kb1dds/AM27S19_eprom_programmer/schematic.kicad_sch

## KiCad design schematic.kicad_sch (2024-02-24)

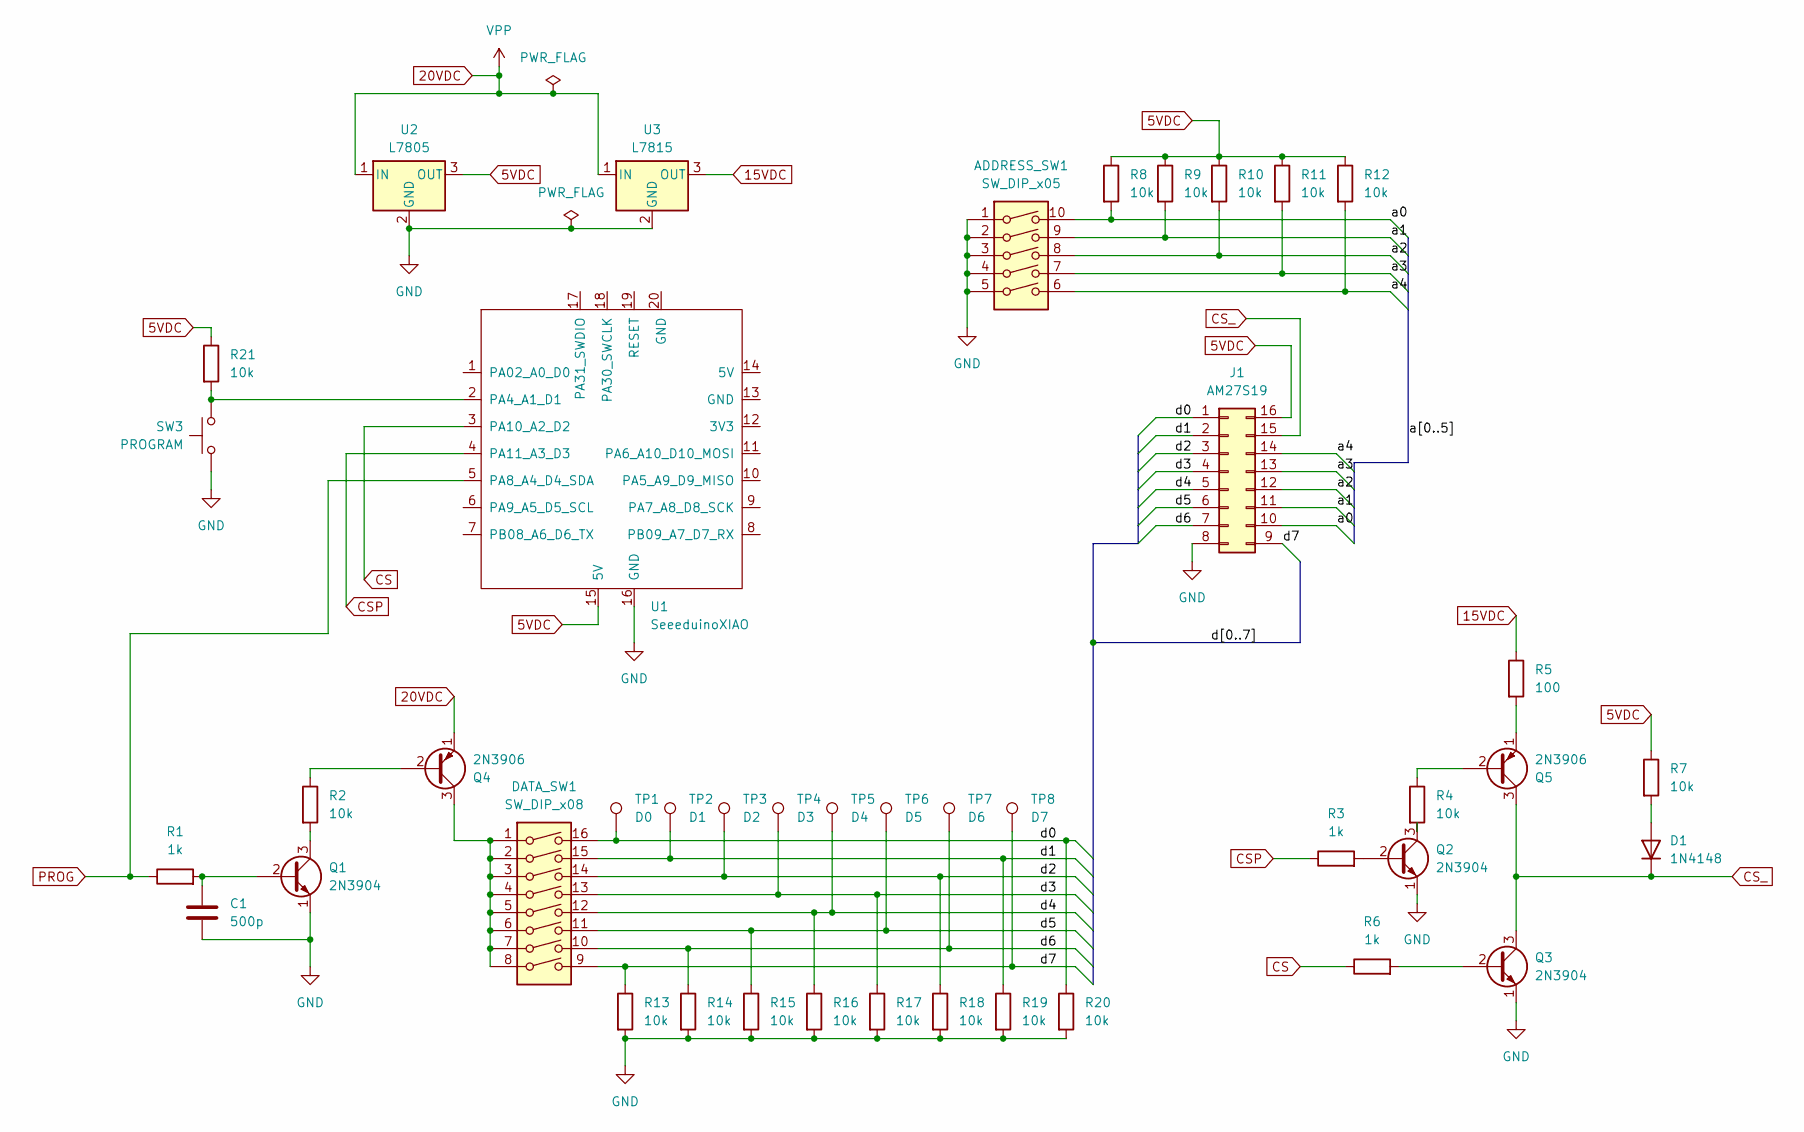
[picture p3: schematic schematic.kicad_sch]

Parts:
ADDRESS_SW1: SW_DIP_x05
C1: 500p
D1: 1N4148; D_DO-35_SOD27_P7.62mm_Horizontal
DATA_SW1: SW_DIP_x08
J1: AM27S19
Q1, Q2, Q3: 2N3904; TO-92_Inline
Q4, Q5: 2N3906; TO-92_Inline
R1, R3, R6: 1k
R2, R4, R7, R8, R9, R10, R11, R12, R13, R14, R15, R16, R17, R18, R19, R20, R21: 10k
R5: 100
SW3: PROGRAM
TP1: D0
TP2: D1
TP3: D2
TP4: D3
TP5: D4
TP6: D5
TP7: D6
TP8: D7
U1: SeeeduinoXIAO
U2: L7805
U3: L7815

Connections:
5VDC: J1.16, R7.1, R8.1, R9.1, R10.1, R11.1, R12.1, R21.1, U1.15 (5V), U2.3 (OUT)
15VDC: R5.1, U3.3 (OUT)
20VDC: Q4.1 (E), U2.1 (IN), U3.1 (IN)
CS: R6.1, U1.3 (PA10_A2_D2)
CSP: R3.1, U1.4 (PA11_A3_D3)
CS_: D1.1 (K), J1.15, Q3.3 (C), Q5.3 (C)
GND: ADDRESS_SW1.1, ADDRESS_SW1.2, ADDRESS_SW1.3, ADDRESS_SW1.4, ADDRESS_SW1.5, C1.2, J1.8, Q1.1 (E), Q2.1 (E), Q3.1 (E), R13.2, R14.2, R15.2, R16.2, R17.2, R18.2, R19.2, R20.2, SW3.2, U1.16 (GND), U2.2 (GND), U3.2 (GND)
unnamed: C1.1, Q1.2 (B), R1.2
unnamed: D1.2 (A), R7.2
unnamed: DATA_SW1.1, DATA_SW1.2, DATA_SW1.3, DATA_SW1.4, DATA_SW1.5, DATA_SW1.6, DATA_SW1.7, DATA_SW1.8, Q4.3 (C)
unnamed: Q1.3 (C), R2.2
unnamed: Q2.2 (B), R3.2
unnamed: Q2.3 (C), R4.2
unnamed: Q3.2 (B), R6.2
unnamed: Q4.2 (B), R2.1
unnamed: Q5.1 (E), R5.2
unnamed: Q5.2 (B), R4.1
unnamed: R21.2, SW3.1, U1.2 (PA4_A1_D1)
PROG: R1.1, U1.5 (PA8_A4_D4_SDA)
a0: ADDRESS_SW1.10, J1.10, R8.2
a1: ADDRESS_SW1.9, J1.11, R9.2
a2: ADDRESS_SW1.8, J1.12, R10.2
a3: ADDRESS_SW1.7, J1.13, R11.2
a4: ADDRESS_SW1.6, J1.14, R12.2
d0: DATA_SW1.16, J1.1, R20.1, TP1.1
d1: DATA_SW1.15, J1.2, R19.1, TP2.1
d2: DATA_SW1.14, J1.3, R18.1, TP3.1
d3: DATA_SW1.13, J1.4, R17.1, TP4.1
d4: DATA_SW1.12, J1.5, R16.1, TP5.1
d5: DATA_SW1.11, J1.6, R15.1, TP6.1
d6: DATA_SW1.10, J1.7, R14.1, TP7.1
d7: DATA_SW1.9, J1.9, R13.1, TP8.1
